WestJeremy/ME507_MicroMouse/Code/Dev/Floodfill/Task_Sensor.h

/** @file Task_Sensor.h
 *  This file contains the header for a task function that takes sensor data
 * 
 *  @author Cesar Santana
 *  @date   2023-Dec-04
*/

#ifndef TASK_SENSOR_H
#define TASK_SENSOR_H

// This is the function that impliments the sensor task
void task_sensor(void* p_params);

#endif
